SeanAlling/MastersProject_Hardware/PrimaryPCB/Images/bottomlayer.png

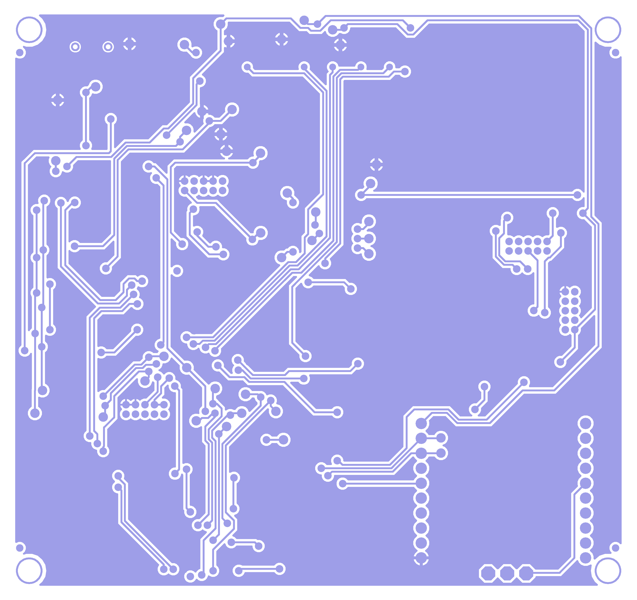
PrimaryPCB/Images/bottomlayer.png
