SeanAlling/MastersProject_Hardware/PrimaryPCB/Images/PCB_Front.png

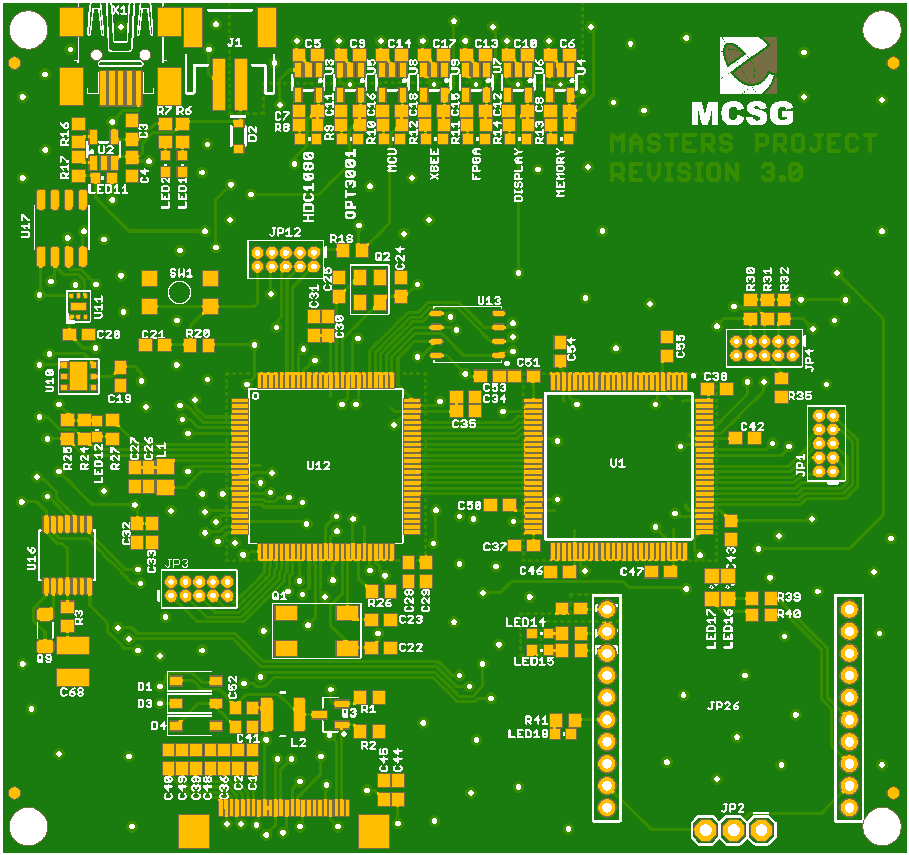
PrimaryPCB/Images/PCB_Front.png
