SeanAlling/MastersProject_Hardware/PrimaryPCB/Images/toplayer.png

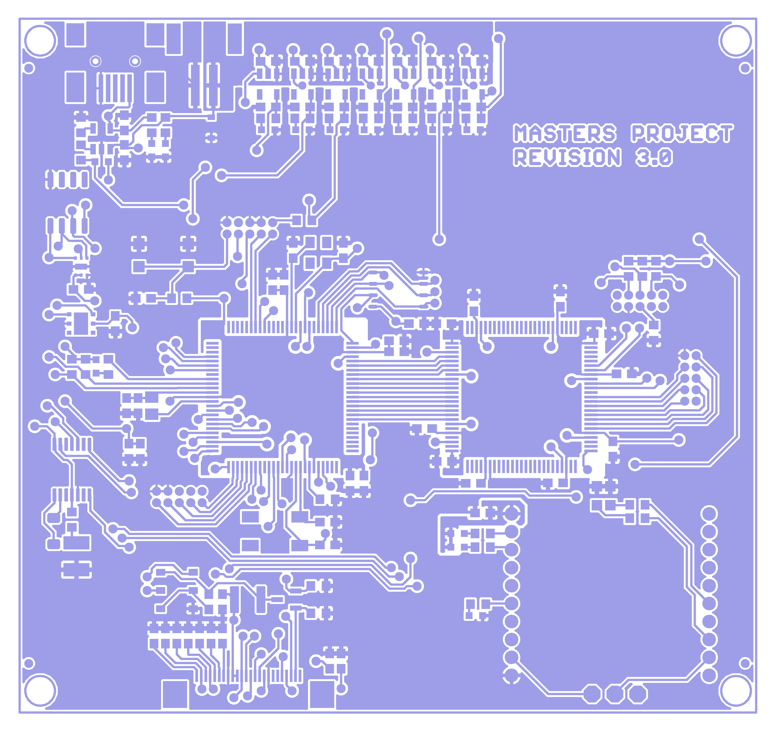
PrimaryPCB/Images/toplayer.png
