SeanAlling/MastersProject_Hardware/PrimaryPCB/Images/toppaste.png

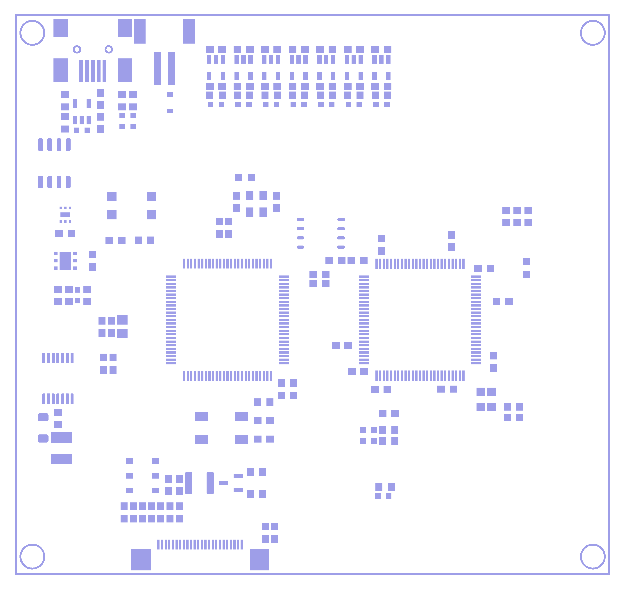
PrimaryPCB/Images/toppaste.png
