SeanAlling/MastersProject_Hardware/PrimaryPCB/Images/topsilkscreen.png

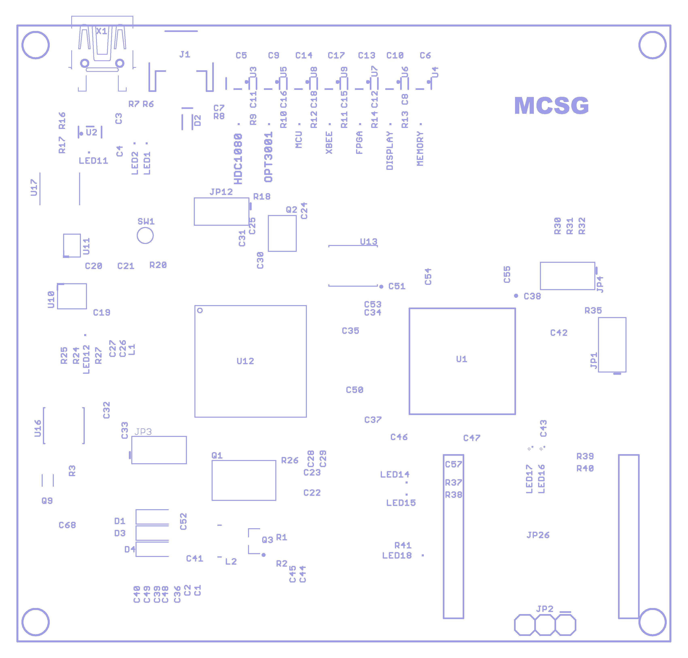
PrimaryPCB/Images/topsilkscreen.png
