SeanAlling/MastersProject_Hardware/PrimaryPCB/Images/bottomassembly.png

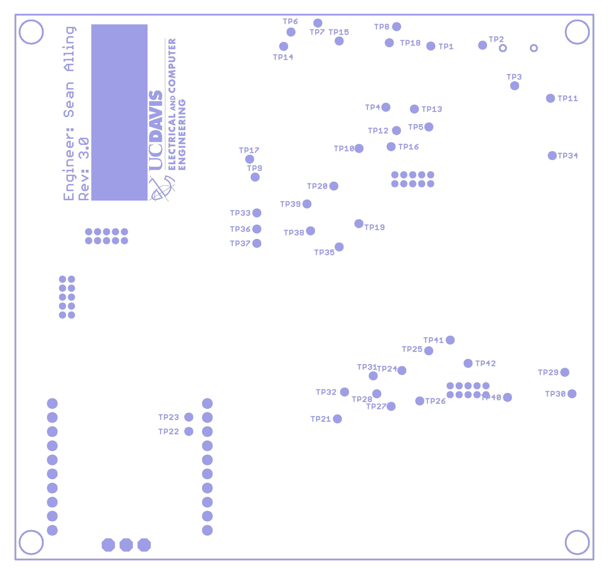
PrimaryPCB/Images/bottomassembly.png
