SeanAlling/MastersProject_Hardware/PrimaryPCB/Images/bottomsoldermask.png

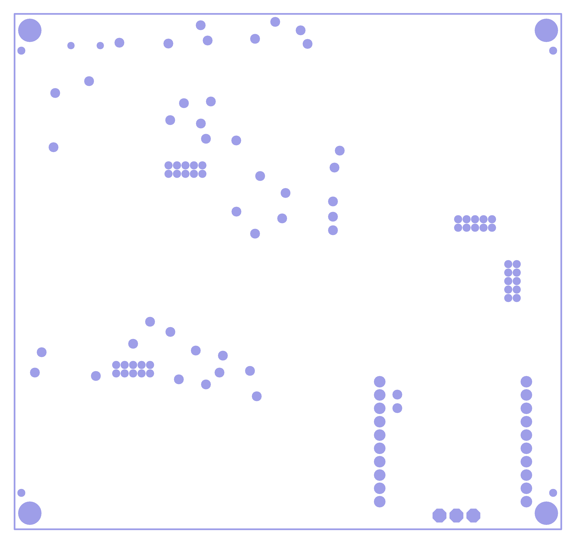
PrimaryPCB/Images/bottomsoldermask.png
