SeanAlling/MastersProject_Hardware/PrimaryPCB/Images/topassembly.png

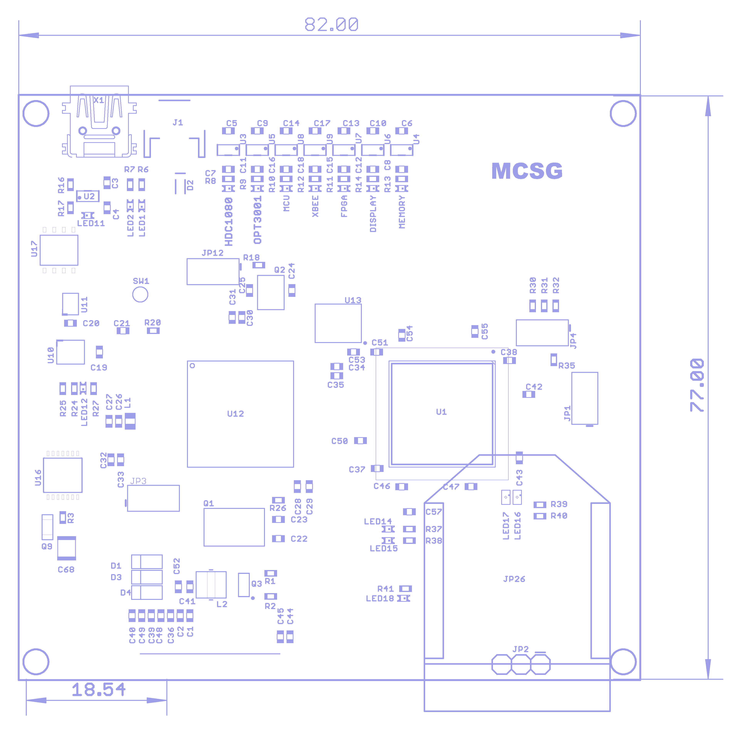
PrimaryPCB/Images/topassembly.png
