SeanAlling/MastersProject_Hardware/PrimaryPCB/Images/topsoldermask.png

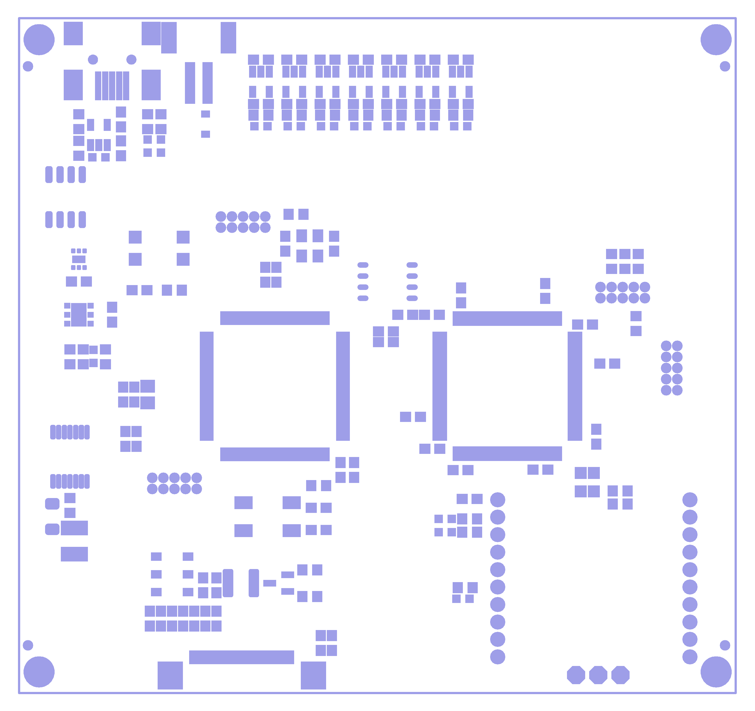
PrimaryPCB/Images/topsoldermask.png
