SeanAlling/MastersProject_Hardware/TestBed/Documentation/Bottom_V1.png

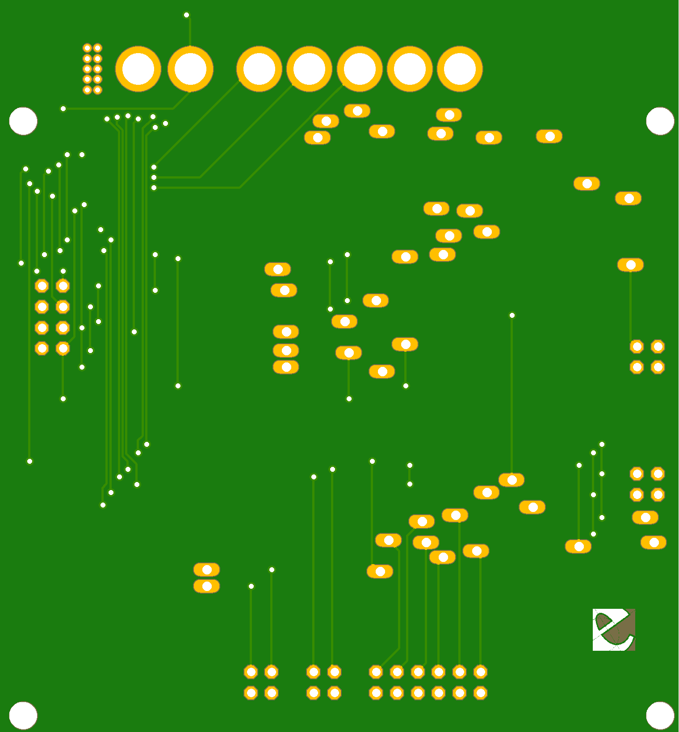
TestBed/Documentation/Bottom_V1.png
