SeanAlling/MastersProject_Hardware/TestBed/Documentation/Front_V1.png

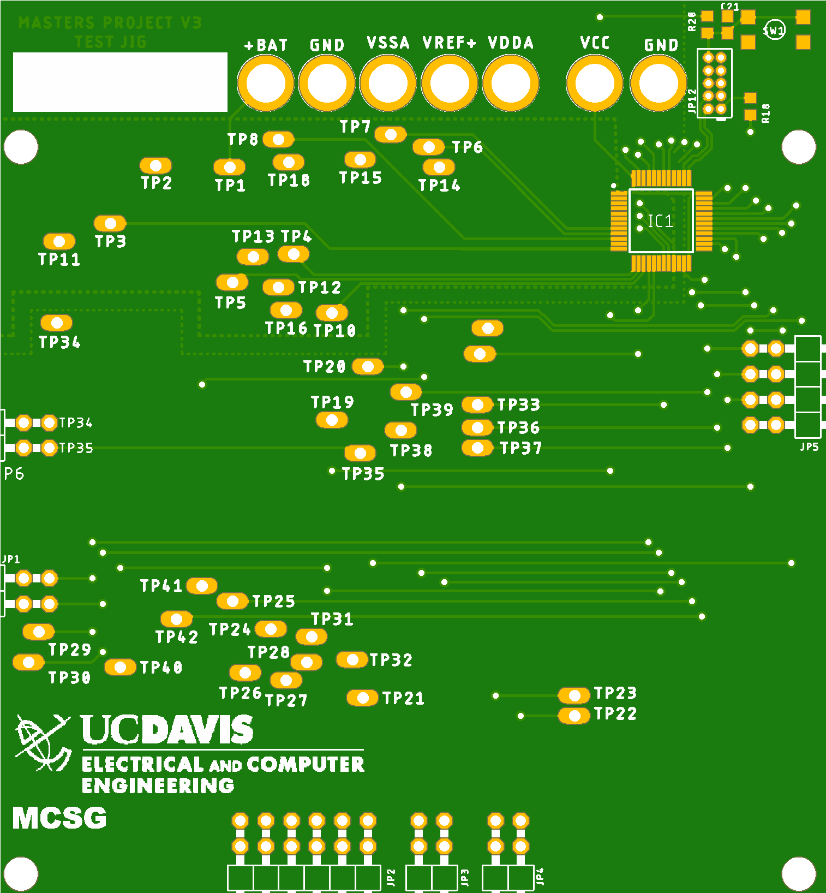
TestBed/Documentation/Front_V1.png
